mercadian/proteus/pcbs/gpio-board/v1.2/Models/61301621821.step

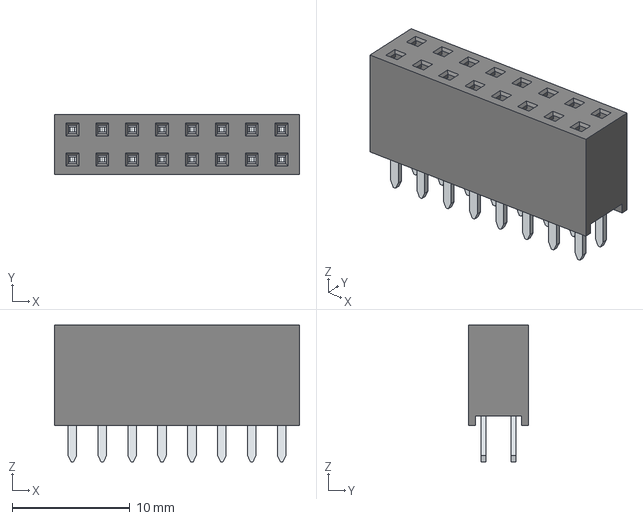
[picture p16: CAD file, 2023-05-07]
pcbs/gpio-board/v1.2/Models/61301621821.step
20.8 x 5.08 x 11.6 mm
