mercadian/proteus/models/v1.0/power-button-holder-bottom.stl

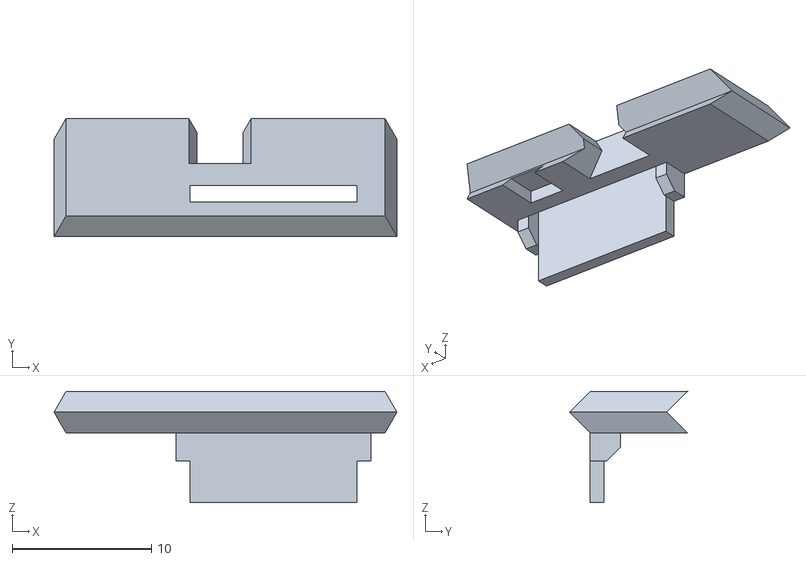
[picture p17: CAD file, 2023-01-21, an earlier design]
models/v1.0/power-button-holder-bottom.stl
24.7 x 8.50 x 8.00
