mercadian/proteus/models/v1.0/power-button-holder-top.stl

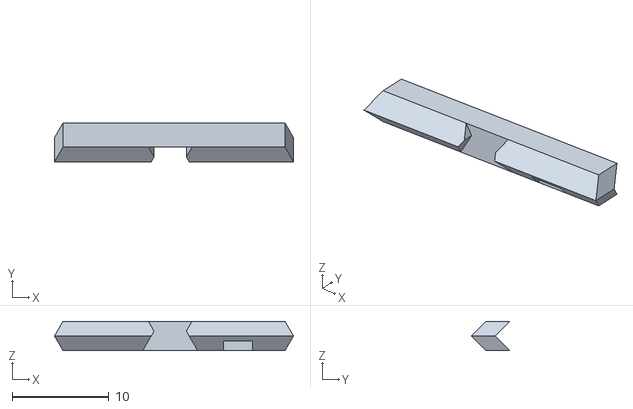
[picture p18: CAD file, 2023-01-21, an earlier design]
models/v1.0/power-button-holder-top.stl
24.7 x 3.97 x 3.00
